trl121/RazerBook13Dock/Inventor/_Photos/Original Top.jpg

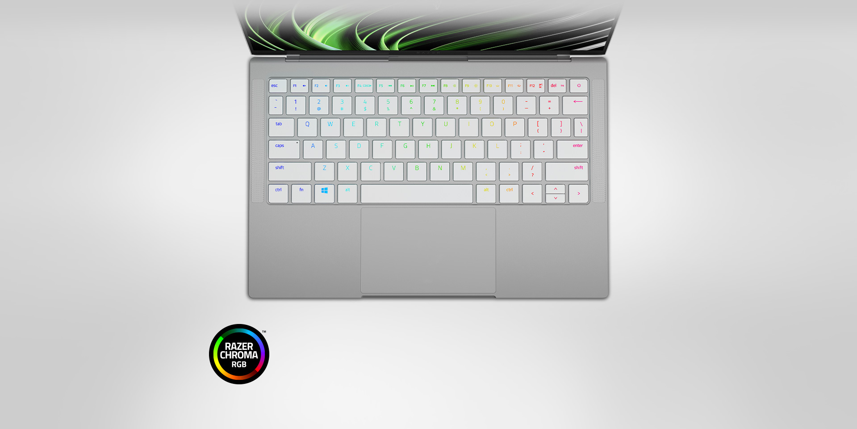
Inventor/_Photos/Original Top.jpg
