trl121/RazerBook13Dock/Inventor/_Photos/Side View 2.jpg

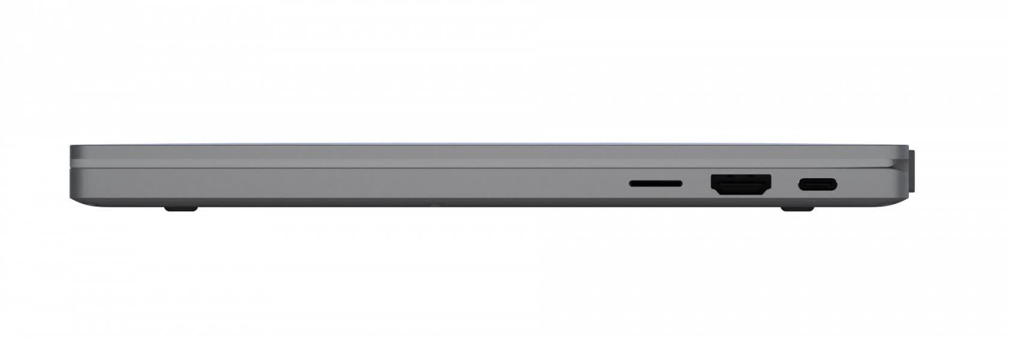
Inventor/_Photos/Side View 2.jpg
