trl121/RazerBook13Dock/photos/Left No Laptop.png

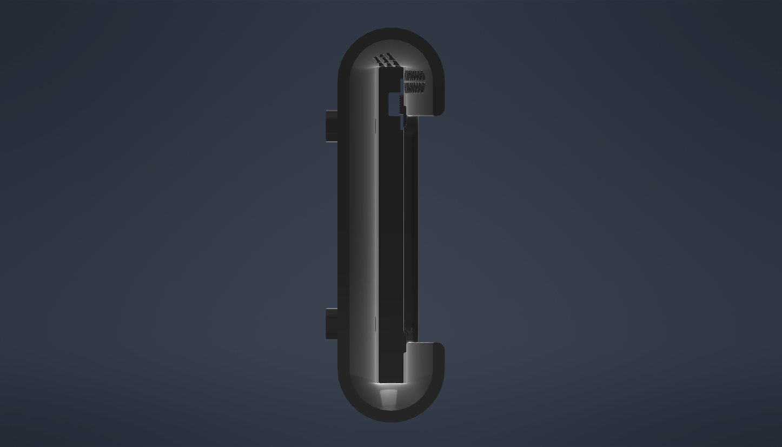
photos/Left No Laptop.png
