trl121/RazerBook13Dock/photos/Rear ISO.png

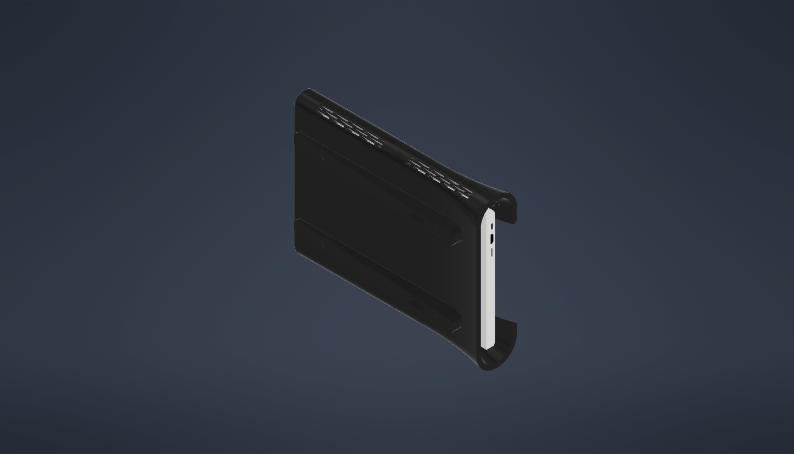
photos/Rear ISO.png
